palthedog/Udong/firmware/include/udong_tusb_config.h

#ifndef UDONG_TUSB_CONFIG_H
#define UDONG_TUSB_CONFIG_H

#define CFG_TUD_HID 1
#define CFG_TUD_CDC 1
#define CFG_TUD_MIDI 0
#define CFG_TUD_MSC 0
#define CFG_TUD_VENDOR 0
#define CFG_TUD_VIDEO 0
#define CFG_TUD_VIDEO_STREAMING 0

// Include other default config.
#include "tusb_config.h"

#endif
